Vitalley/MiniTrip/FIRMWARE/config.h

#include <xc.h>
#define _XTAL_FREQ 32000000
#define I2C_SPEED 100
#define ft_mult 570
#define ft_sdd 370
#define array_size_voltage 8
#define array_size_fuel 64
#define impulse_per_litre 22500
#define OLED_Adr 0x3C
