Vitalley/MiniTrip/FIRMWARE/EEPROM.h

unsigned long int erd(unsigned char eeadr);
void ewr(unsigned long int dt,unsigned char eeadr);
void ewr2(unsigned long int dt,unsigned char eeadr);
void EEREADDATA(void);
void EEWRITEFATA(void);
void EETRIPRESET(void);
void EETO1RESET(void);
void EETO2RESET(void);
