Vitalley/MiniTrip/FIRMWARE/Screens.h

#include <xc.h>
void screen0(void);
void screen1(void);
void screen2(void);
void screen3(void);
void screen4(void);
void screen5(void);
void screen6(void);
void screen7(void);
void screen8(void);
void screen9(void);
void screen10(void);
void screen11(void);
void screen12(void);
void screen13(void);
